abhaybd/opensaber/code/include/IgnitionSound.h

#pragma once

constexpr uint igniteTime = 524288; // micros, is a power of two (for faster division)

constexpr struct {
    const uint freq = 12000; // Hz
    const uint precision = 16;
    const uint16_t sound[14482] = {32768, 32872, 32888, 32831, 32735, 32645, 32551, 32518, 32472, 32410, 32351, 32471, 32541, 32473, 32406, 32448, 32561, 32672, 32607, 32522, 32507, 32546, 32605, 32475, 32472, 32618, 32596, 32638, 32650, 32490, 32698, 32762, 32599, 32683, 32706, 32747, 32746, 32561, 32608, 32737, 32718, 32768, 32692, 32787, 32839, 32818, 32884, 32935, 32988, 33052, 32972, 32829, 32851, 32743, 32766, 32710, 32671, 32816, 32841, 32706, 32766, 32726, 32710, 32807, 32618, 32676, 32684, 32701, 32649, 32657, 32755, 32815, 32715, 32633, 32597, 32603, 32621, 32447, 32578, 32567, 32597, 32681, 32639, 32620, 32713, 32718, 32813, 32900, 32782, 32845, 32762, 32729, 32792, 32873, 32975, 32998, 33044, 33145, 33220, 33231, 33254, 33196, 33232, 33255, 33088, 33199, 33133, 33108, 33254, 33238, 33330, 33395, 33325, 33382, 33437, 33444, 33458, 33306, 33262, 33139, 32955, 33015, 32896, 32827, 32854, 32814, 32945, 33054, 33120, 33168, 33267, 33305, 33458, 33500, 33531, 33562, 33490, 33538, 33633, 33614, 33550, 33541, 33582, 33555, 33489, 33463, 33261, 33232, 33064, 32910, 32990, 32985, 32990, 33127, 33092, 33161, 33266, 33150, 33205, 33156, 33124, 33171, 33160, 33055, 33043, 32940, 32826, 32879, 32824, 32876, 32876, 32921, 32996, 33077, 33058, 32948, 33018, 33026, 32999, 32967, 32917, 32906, 32934, 33004, 32897, 32916, 32962, 32972, 33155, 33035, 32954, 33172, 33230, 33126, 33044, 32892, 32920, 33052, 32994, 33003, 33091, 33132, 33224, 33110, 32972, 32956, 32914, 32846, 32696, 32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
} ignitionSound;
