abhaybd/opensaber/code/include/Extinguish.h

#pragma once

const uint extinguishStart = 200000; // micros
const uint extinguishEnd = 1070000;

constexpr struct {
    const uint freq = 12000; // Hz
    const uint precision = 16;
    const uint16_t sound[13921] = {34749, 35191, 34984, 34794, 34934, 35091, 34947, 34727, 34840, 35006, 34860, 34698, 34684, 34646, 34581, 34375, 34138, 33941, 33819, 33806, 33615, 33268, 33202, 33040, 32839, 32842, 33043, 33052, 32676, 32516, 32465, 32432, 32396, 32335, 32052, 31798, 31771, 31960, 32040, 31769, 31551, 31484, 31388, 31342, 31240, 31022, 30956, 31041, 31124, 31003, 30946, 31169, 31188, 31079, 31009, 31123, 31384, 31431, 31291, 31373, 31523, 31612, 31695, 31714, 31798, 31828, 31781, 31829, 31800, 31782, 31776, 31603, 31399, 31339, 31227, 31045, 30791, 30705, 30614, 30345, 30242, 30138, 29982, 29919, 30021, 30044, 29976, 30093, 30235, 30298, 30394, 30700, 31016, 31127, 31245, 31533, 31941, 32303, 32676, 33018, 33252, 33540, 33919, 34211, 34436, 34583, 34643, 34723, 34802, 34916, 35071, 34918, 34645, 34682, 34728, 34687, 34546, 34320, 34282, 34367, 34339, 34219, 34080, 34011, 34024, 34018, 34138, 34315, 34399, 34253, 34094, 34243, 34488, 34664, 34588, 34439, 34442, 34705, 34894, 34875, 34800, 34750, 34833, 34835, 34836, 34762, 34550, 34207, 33979, 34062, 34315, 34207, 33660, 33287, 33177, 33117, 33418, 33601, 33045, 32571, 32488, 32611, 32753, 32827, 32582, 32064, 31788, 31914, 32346, 32201, 31168, 30663, 30982, 31378, 31706, 32149, 32564, 32628, 32525, 32285, 31945, 31712, 31671, 31495, 31169, 30954, 30991, 30964, 30541, 30410, 30594, 30719, 30641, 30695, 30855, 30703, 30616, 30702, 30982, 31295, 31213, 30982, 31085, 31338, 31190, 30740, 30619, 30893, 30974, 30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
} extinguishSound;
